PowerBroker2/UniversalTransmitter/extras/docs/4.jpg

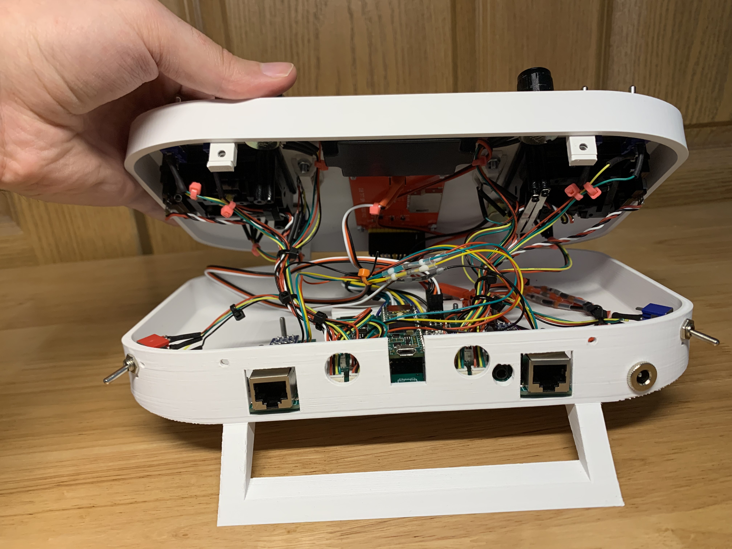
extras/docs/4.jpg
