PowerBroker2/UniversalTransmitter/examples/complex_example/SaveButton.h

#pragma once




const int SAVE_BUTTON_W = 40;
const int SAVE_BUTTON_H = 40;




const uint16_t saveButtonPixMap [SAVE_BUTTON_H * SAVE_BUTTON_W] PROGMEM = {
0x8410, 0x8410, 0x8410, 0x8410, 0x8410, 0x8410, 0x8410, 0x8410, 0x8410, 0x8410, 0x8410, 0x8410, 0x8410, 0x8410, 0x8410, 0x8410, 0x8410, 0x8410, 0x8410, 0x8410, 0x8410, 0x8410, 0x8410, 0x8410, 0x8410, 0x8410, 0x8410, 0x8410, 0x8410, 0x8410, 0x8410, 0x8410, 0x8410, 0x8410, 0x8410, 0x8410, 0x8410, 0x8410, 0x8410, 0x8410, 
0x8410, 0x8410, 0x8410, 0x8410, 0x8410, 0x8410, 0x8410, 0x8410, 0x8410, 0x8410, 0x8410, 0x8410, 0x8410, 0x8410, 0x8410, 0x8410, 0x8410, 0x8410, 0x8410, 0x8410, 0x8410, 0x8410, 0x8410, 0x8410, 0x8410, 0x8410, 0x8410, 0x8410, 0x8410, 0x8410, 0x8410, 0x8410, 0x8410, 0x8410, 0x8410, 0x8410, 0x8410, 0x8410, 0x8410, 0x8410, 
0x8410, 0x8410, 0x8410, 0x8410, 0x8410, 0x7bf0, 0x7bf0, 0x840f, 0x840f, 0x840f, 0x840f, 0x840f, 0x840f, 0x840f, 0x840f, 0x840f, 0x840f, 0x840f, 0x840f, 0x840f, 0x840f, 0x840f, 0x840f, 0x840f, 0x840f, 0x840f, 0x840f, 0x840f, 0x840f, 0x840f, 0x840f, 0x840f, 0x840f, 0x7bf0, 0x8410, 0x8410, 0x8410, 0x8410, 0x8410, 0x8410, 
0x8410, 0x8410, 0x8410, 0x8410, 0x7bf0, 0x840f, 0x8c4f, 0x842f, 0x842f, 0x842f, 0x842f, 0x842f, 0x842f, 0x842f, 0x842f, 0x842f, 0x842f, 0x842f, 0x842f, 0x842f, 0x842f, 0x842f, 0x842f, 0x842f, 0x842f, 0x842f, 0x842f, 0x842f, 0x842f, 0x842f, 0x842f, 0x842f, 0x8c4f, 0x842f, 0x7bf0, 0x7bf0, 0x8410, 0x8410, 0x8410, 0x8410, 
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
0,0,0,0,0,0,0,0,0,0,0,0,0,0,0,0,0,0,0,0,0,0,0,0,0,0,0,0,0,0,0,0,0,0,0,0,0,0,0,0,
0,0,0,0,0,0,0,0,0,0,0,0,0,0,0,0,0,0,0,0,0,0,0,0,0,0,0,0,0,0,0,0,0,0,0,0,0,0,0,0,
0,0,0,0,0,0,0,0,0,0,0,0,0,0,0,0,0,0,0,0,0,0,0,0,0,0,0,0,0,0,0,0,0,0,0,0,0,0,0,0
};
