PowerBroker2/UniversalTransmitter/examples/complex_example/button.h

#pragma once




const int BUTTON_W = 89;
const int BUTTON_H = 40;




const uint16_t buttonPixMap [BUTTON_H * BUTTON_W] PROGMEM = {
0x8410, 0x8410, 0x8410, 0x8410, 0x8410, 0x8410, 0x7bef, 0x8410, 0x7bef, 0x7bef, 0x8c51, 0x9492, 0x7bef, 0x4a69, 0x2104, 0x0020, 0x0000, 0x0000, 0x0000, 0x0000, 0x0000, 0x0000, 0x0000, 0x0000, 0x0000, 0x0000, 0x0000, 0x0000, 0x0000, 0x0000, 0x0000, 0x0000, 0x0000, 0x0000, 0x0000, 0x0000, 0x0000, 0x0000, 0x0000, 0x0000, 0x0000, 0x0000, 0x0000, 0x0000, 0x0000, 0x0000, 0x0000, 0x0000, 0x0000, 0x0000, 0x0000, 0x0000, 0x0000, 0x0000, 0x0000, 0x0000, 0x0000, 0x0000, 0x0000, 0x0000, 0x0000, 0x0000, 0x0000, 0x0000, 0x0000, 0x0000, 0x0000, 0x0000, 0x0000, 0x0000, 0x0000, 0x0000, 0x0000, 0x0020, 0x2104, 0x4a69, 0x7bef, 0x9492, 0x8c51, 0x7bef, 0x7bef, 0x8410, 0x7bef, 0x8410, 0x8410, 0x8410, 0x8410, 0x8410, 0x8410, 
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
0,0,0,0,0,0,0,0,0,0,0,0,0,0,0,0,0,0,1,1,1,1,1,1,1,1,1,1,1,1,1,1,1,1,1,1,1,1,1,1,1,1,1,1,1,1,1,1,1,1,1,1,1,1,1,1,1,1,1,1,1,1,1,1,1,1,1,1,1,1,1,0,0,0,0,0,0,0,0,0,0,0,0,0,0,0,0,0,0
};
