PowerBroker2/UniversalTransmitter/examples/complex_example/wide_button.h

#pragma once




const int WIDE_BUTTON_W = 180;
const int WIDE_BUTTON_H = 40;




const uint16_t wideButtonPixMap [WIDE_BUTTON_H * WIDE_BUTTON_W] PROGMEM = {
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
};
