PowerBroker2/UniversalTransmitter/examples/complex_example/CheckButton.h

#pragma once




const int CHECK_BUTTON_W = 20;
const int CHECK_BUTTON_H = 20;




const uint16_t checkButtonPixMap [CHECK_BUTTON_H * CHECK_BUTTON_W] PROGMEM = {
0x8410, 0x8410, 0x8410, 0x8410, 0x8410, 0x8410, 0x8410, 0x8410, 0x8410, 0x8410, 0x8410, 0x8410, 0x8410, 0x8410, 0x8410, 0x7bef, 0x8410, 0x9cf3, 0x5acb, 0x18c3, 
0x8410, 0x8410, 0x8410, 0x8410, 0x8410, 0x8410, 0x8410, 0x8410, 0x8410, 0x8410, 0x8410, 0x8410, 0x8410, 0x8410, 0x7bef, 0x8410, 0x8c71, 0x4228, 0x18e3, 0x73ae, 
0x8410, 0x8410, 0x8410, 0x8410, 0x8410, 0x8410, 0x8410, 0x8410, 0x8410, 0x8410, 0x8410, 0x8410, 0x8410, 0x7bef, 0x8430, 0x8bf1, 0x29c5, 0x0080, 0x7bcf, 0x9492, 
0x8410, 0x8410, 0x8410, 0x8410, 0x8410, 0x8410, 0x8410, 0x8410, 0x8410, 0x8410, 0x8410, 0x8410, 0x7bef, 0x8c51, 0x8390, 0x1a03, 0x0160, 0x7bcf, 0x8c51, 0x7bef, 
0x8410, 0x8410, 0x8410, 0x8410, 0x8410, 0x8410, 0x8410, 0x8410, 0x8410, 0x8410, 0x8410, 0x7bef, 0x8c51, 0x7b4f, 0x1242, 0x0240, 0x734e, 0x8c51, 0x7bef, 0x8410, 
0x8410, 0x8410, 0x8410, 0x8410, 0x8410, 0x8410, 0x8410, 0x8410, 0x8410, 0x8410, 0x7bef, 0x8c51, 0x7b2f, 0x1262, 0x0300, 0x62ac, 0x8c51, 0x7bef, 0x8410, 0x8410, 
0x8410, 0x8410, 0x8410, 0x8410, 0x8410, 0x8410, 0x8410, 0x8410, 0x8410, 0x7bef, 0x8450, 0x7b4f, 0x1242, 0x03e0, 0x4a29, 0x9451, 0x7bef, 0x8410, 0x8410, 0x8410, 
0x8410, 0x8410, 0x8410, 0x8410, 0x8410, 0x8410, 0x8410, 0x8410, 0x7bef, 0x8430, 0x83b0, 0x1a03, 0x04c0, 0x2a05, 0x8c11, 0x8410, 0x7bef, 0x8410, 0x8410, 0x8410, 
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
0,0,118,255,247,146,255,255,255,50,0,0,0,0,0,0,0,0,0,0,
0,0,0,168,255,255,255,255,186,0,0,0,0,0,0,0,0,0,0,0,
0,0,0,0,216,255,255,255,43,0,0,0,0,0,0,0,0,0,0,0,
0,0,0,0,27,247,255,184,0,0,0,0,0,0,0,0,0,0,0,0,
0,0,0,0,0,67,245,51,0,0,0,0,0,0,0,0,0,0,0,0,
0,0,0,0,0,0,133,2,0,0,0,0,0,0,0,0,0,0,0,0
};
