PowerBroker2/UniversalTransmitter/examples/complex_example/DownButton.h

#pragma once




const int DOWN_BUTTON_W = 20;
const int DOWN_BUTTON_H = 20;




const uint16_t downButtonPixMap [DOWN_BUTTON_H * DOWN_BUTTON_W] PROGMEM = {
0x8410, 0x8410, 0x8410, 0x8410, 0x8410, 0x7bf0, 0x840f, 0x942f, 0x8bee, 0x738e, 0x738d, 0x83ce, 0x942f, 0x8c0f, 0x7bf0, 0x8410, 0x8410, 0x8410, 0x8410, 0x8410, 
0x8410, 0x8410, 0x8410, 0x7bf0, 0x8410, 0x8c0f, 0x6b8e, 0x536f, 0x53d2, 0x5c34, 0x5c54, 0x53f3, 0x5390, 0x636e, 0x83ef, 0x840f, 0x7bf0, 0x8410, 0x8410, 0x8410, 
0x8410, 0x8410, 0x7bf0, 0x840f, 0x7bcf, 0x4350, 0x6cd6, 0xae7c, 0xbefe, 0xbf1f, 0xaede, 0xa69d, 0x9e3c, 0x7538, 0x4bb1, 0x73ae, 0x8c0f, 0x7bf0, 0x8410, 0x8410, 
0x8410, 0x7bf0, 0x840f, 0x73ae, 0x4392, 0xae7c, 0xdf9f, 0xbf1f, 0x9e9d, 0x8e3d, 0x7dfc, 0x6dbc, 0x6dbc, 0x7dfc, 0x963c, 0x5c54, 0x638e, 0x8c0f, 0x7bf0, 0x8410, 
0x8410, 0x840f, 0x7bce, 0x4392, 0xc71e, 0xc75f, 0x9e9d, 0x967d, 0x863d, 0x7dfc, 0x6dbb, 0x5d7b, 0x553a, 0x3cd9, 0x2c99, 0x861c, 0x5c75, 0x6b8e, 0x840f, 0x7bf0, 
0x7bf0, 0x8c0f, 0x4350, 0xa67c, 0xbf3f, 0x967d, 0x8e5d, 0x861c, 0x75dc, 0x659b, 0x5d5b, 0x4d1a, 0x3499, 0x1c38, 0x0bf7, 0x03b6, 0x7ddb, 0x53d2, 0x83ef, 0x7bf0, 
0x840f, 0x6b8e, 0x6cb6, 0xc75f, 0x8e5d, 0x861d, 0x75dc, 0x6dbc, 0x657b, 0x553a, 0x2c99, 0x1418, 0x0bf7, 0x03b6, 0x0396, 0x0395, 0x2437, 0x7d59, 0x5b6f, 0x8c2f, 
0x942f, 0x536f, 0x9e5c, 0x9e9e, 0x7dfc, 0x75fc, 0x7dfc, 0x4d3a, 0x44fa, 0x1438, 0x03f7, 0x0bf7, 0x0396, 0x2457, 0x1c17, 0x0375, 0x0354, 0x6559, 0x63f2, 0x940e, 
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
0,0,0,38,237,255,255,255,255,255,255,255,255,255,255,255,78,0,0,0,
0,0,0,0,27,190,255,255,255,255,255,255,255,255,216,57,0,0,0,0,
0,0,0,0,0,0,71,170,224,241,242,230,185,93,0,0,0,0,0,0,
0,0,0,0,0,0,0,0,0,33,37,3,0,0,0,0,0,0,0,0
};
