PowerBroker2/UniversalTransmitter/examples/complex_example/LeftButton.h

#pragma once




const int LEFT_BUTTON_W = 20;
const int LEFT_BUTTON_H = 20;




const uint16_t leftButtonPixMap [LEFT_BUTTON_H * LEFT_BUTTON_W] PROGMEM = {
0x8410, 0x8410, 0x8410, 0x8410, 0x8410, 0x7bf0, 0x840f, 0x942f, 0x8bee, 0x7bae, 0x7bae, 0x8bee, 0x942f, 0x840f, 0x7bf0, 0x8410, 0x8410, 0x8410, 0x8410, 0x8410, 
0x8410, 0x8410, 0x8410, 0x7bf0, 0x8410, 0x8c0f, 0x6b8e, 0x536f, 0x53b2, 0x5c13, 0x5c13, 0x53d2, 0x5390, 0x6b8e, 0x8c0f, 0x8410, 0x7bf0, 0x8410, 0x8410, 0x8410, 
0x8410, 0x8410, 0x7bf0, 0x840f, 0x7bcf, 0x4350, 0x64b6, 0xa65c, 0xbefe, 0xb6fe, 0xaede, 0xa69d, 0x961b, 0x6cf7, 0x4b90, 0x73ae, 0x840f, 0x7bf0, 0x8410, 0x8410, 
0x8410, 0x7bf0, 0x840f, 0x73ae, 0x4392, 0xae7c, 0xdf9f, 0xbf3f, 0x9e9e, 0x8e3d, 0x7dfc, 0x6ddc, 0x6ddc, 0x861c, 0x961c, 0x5413, 0x6b8e, 0x840f, 0x7bf0, 0x8410, 
0x8410, 0x840f, 0x7bce, 0x4392, 0xc71e, 0xc75f, 0x9e9d, 0x967d, 0x8e3d, 0x75dc, 0x659b, 0x555a, 0x553a, 0x3cb9, 0x34b9, 0x8e1c, 0x5414, 0x73ae, 0x840f, 0x7c10, 
0x7bf0, 0x8c0f, 0x4350, 0xae9d, 0xbf3f, 0x967d, 0x8e5d, 0x861c, 0x6dbc, 0x555b, 0xbedd, 0xae9d, 0x2c99, 0x1c38, 0x0bf7, 0x0bd6, 0x7ddb, 0x53b1, 0x83ef, 0x7bf0, 
0x840f, 0x636e, 0x6cd7, 0xc75f, 0x8e5d, 0x863d, 0x7dfc, 0x659b, 0x4d3a, 0xaebd, 0xffff, 0xe79e, 0x1c38, 0x03b6, 0x0bd6, 0x0375, 0x2c78, 0x7538, 0x638f, 0x8c0f, 
0x942f, 0x5370, 0xa67c, 0x9e9e, 0x861d, 0x75dc, 0x659b, 0x451a, 0xa69d, 0xffdf, 0xdf7e, 0x2c78, 0x03b6, 0x0bd6, 0x0bd6, 0x0bb5, 0x0374, 0x6d79, 0x63d1, 0x942f, 
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
0,0,0,57,250,255,255,255,255,255,255,255,255,255,255,255,76,0,0,0,
0,0,0,0,44,209,255,255,255,255,255,255,255,255,219,58,0,0,0,0,
0,0,0,0,0,0,90,187,233,245,246,235,193,100,1,0,0,0,0,0,
0,0,0,0,0,0,0,0,11,51,53,15,0,0,0,0,0,0,0,0
};
