PowerBroker2/UniversalTransmitter/examples/complex_example/RightButton.h

#pragma once




const int RIGHT_BUTTON_W = 20;
const int RIGHT_BUTTON_H = 20;




const uint16_t rightButtonPixMap [RIGHT_BUTTON_H * RIGHT_BUTTON_W] PROGMEM = {
0x8410, 0x8410, 0x8410, 0x8410, 0x7c10, 0x7bf0, 0x8c0f, 0x940f, 0x738e, 0x5b2d, 0x530d, 0x634d, 0x8bee, 0x942f, 0x8410, 0x7bf0, 0x8410, 0x8410, 0x8410, 0x8410, 
0x8410, 0x8410, 0x8410, 0x7bf0, 0x8410, 0x83ef, 0x5b6e, 0x4b91, 0x5c34, 0x6cb6, 0x6cd6, 0x6475, 0x53f2, 0x536f, 0x7bce, 0x8c0f, 0x7bf0, 0x8410, 0x8410, 0x8410, 
0x8410, 0x8410, 0x7bf0, 0x840f, 0x73ae, 0x4371, 0x7d58, 0xbefe, 0xc73f, 0xbf1f, 0xaefe, 0xa6be, 0x9e7d, 0x8dda, 0x5434, 0x5b6f, 0x8c0f, 0x7bf0, 0x8410, 0x8410, 
0x8410, 0x7bf0, 0x840f, 0x6b8e, 0x43d3, 0xbefe, 0xd79f, 0xaefe, 0x965d, 0x861c, 0x7dfc, 0x6d9b, 0x5d7b, 0x65bb, 0x8e3d, 0x6cf7, 0x536f, 0x8c0f, 0x7bf0, 0x8410, 
0x8410, 0x840f, 0x7bce, 0x43b2, 0xcf5f, 0xbf3f, 0x9e7d, 0x965d, 0x861c, 0x7dfc, 0x659b, 0x5d7b, 0x553a, 0x3cd9, 0x1c58, 0x659b, 0x6d18, 0x5b6f, 0x8c0f, 0x7bf0, 
0x7bf0, 0x8c0f, 0x4350, 0xae9d, 0xbf3f, 0x967d, 0x8e3d, 0x7dfc, 0xc71e, 0xcf3e, 0x555a, 0x3cd9, 0x2c98, 0x1437, 0x0bf7, 0x0375, 0x657a, 0x6454, 0x73ae, 0x840f, 
0x840f, 0x6b8e, 0x64b6, 0xc75f, 0x8e3d, 0x863d, 0x75dc, 0x6dbb, 0xcf1e, 0xf7df, 0xbedd, 0x1418, 0x03b6, 0x0bd7, 0x0bd6, 0x03b6, 0x0bd6, 0x7d9a, 0x5b90, 0x942f, 
0x942f, 0x536f, 0x9e3b, 0x9e9e, 0x7e1d, 0x6ddc, 0x659b, 0x553b, 0x34da, 0xae9d, 0xf7df, 0xbedd, 0x0bd7, 0x0396, 0x0bd6, 0x0bb5, 0x0334, 0x5519, 0x6454, 0x83ae, 
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
0,0,0,187,255,255,255,255,255,255,255,255,255,255,255,255,253,36,0,0,
0,0,0,4,193,255,255,255,255,255,255,255,255,255,255,247,62,0,0,0,
0,0,0,0,0,136,252,255,255,255,255,255,255,255,192,37,0,0,0,0,
0,0,0,0,0,0,27,118,187,218,222,202,149,61,0,0,0,0,0,0,
0,0,0,0,0,0,0,0,0,0,0,0,0,0,0,0,0,0,0,0
};
