PowerBroker2/UniversalTransmitter/examples/complex_example/UpButton.h

#pragma once




const int UP_BUTTON_W = 20;
const int UP_BUTTON_H = 20;




const uint16_t upButtonPixMap [UP_BUTTON_H * UP_BUTTON_W] PROGMEM = {
0x8410, 0x8410, 0x8410, 0x8410, 0x8410, 0x7bf0, 0x840f, 0x942f, 0x83ce, 0x6b6d, 0x6b6d, 0x7bae, 0x942f, 0x8c0f, 0x7bf0, 0x7c10, 0x8410, 0x8410, 0x8410, 0x8410, 
0x8410, 0x8410, 0x8410, 0x7bf0, 0x8410, 0x8c0f, 0x636e, 0x4b70, 0x53f2, 0x5c54, 0x6454, 0x5c13, 0x5390, 0x636e, 0x83ef, 0x840f, 0x7bf0, 0x8410, 0x8410, 0x8410, 
0x8410, 0x8410, 0x7bf0, 0x840f, 0x73ae, 0x4350, 0x7517, 0xb69d, 0xbf1e, 0xbf1f, 0xaede, 0xa69e, 0x9e5c, 0x7d38, 0x4bb1, 0x73ae, 0x8c0f, 0x7bf0, 0x8410, 0x8410, 
0x8410, 0x7bf0, 0x840f, 0x6b8e, 0x43b3, 0xb6bd, 0xdf9f, 0xb71f, 0x9e7d, 0x863d, 0x7dfc, 0x6dbb, 0x659b, 0x7dfc, 0x963c, 0x5c55, 0x638e, 0x8c0f, 0x7bf0, 0x8410, 
0x8410, 0x840f, 0x7bae, 0x43b3, 0xcf5f, 0xc73f, 0x9e7d, 0x965d, 0x863c, 0x7dfc, 0x6dbb, 0x5d7b, 0x553a, 0x3cb9, 0x2c98, 0x861c, 0x5c55, 0x6b8e, 0x840f, 0x7bf0, 
0x7bf0, 0x8c0f, 0x4350, 0xb6bd, 0xbf1f, 0x967d, 0x8e5d, 0x7e1c, 0x75dc, 0x5d5b, 0x4d1a, 0x44fa, 0x2c99, 0x1c38, 0x0bf7, 0x03b6, 0x7ddb, 0x53d2, 0x83ef, 0x7bf0, 
0x840f, 0x636e, 0x6cf7, 0xc75f, 0x8e5d, 0x863d, 0x75fc, 0x6dbc, 0x4d1a, 0x7dfc, 0x7ddb, 0x03b7, 0x0bf7, 0x0bd7, 0x0bd6, 0x0395, 0x2457, 0x7d58, 0x636f, 0x8c0f, 
0x942f, 0x5370, 0xa67c, 0x969e, 0x7e1d, 0x75dc, 0x659b, 0x44fa, 0x659b, 0xdf7e, 0xefbf, 0x5d5a, 0x0376, 0x0bd6, 0x0bd6, 0x0bb5, 0x0354, 0x6d59, 0x63f2, 0x940f, 
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
0,0,0,38,236,255,255,255,255,255,255,255,255,255,255,251,63,0,0,0,
0,0,0,0,26,187,255,255,255,255,255,255,255,255,204,44,0,0,0,0,
0,0,0,0,0,0,66,164,220,237,238,223,174,80,0,0,0,0,0,0,
0,0,0,0,0,0,0,0,0,21,24,0,0,0,0,0,0,0,0,0
};
