PowerBroker2/UniversalTransmitter/examples/complex_example/XButton.h

#pragma once




const int X_BUTTON_W = 20;
const int X_BUTTON_H = 20;




const uint16_t xButtonPixMap [X_BUTTON_H * X_BUTTON_W] PROGMEM = {
0x8410, 0x7bef, 0x8410, 0x8492, 0x1186, 0x6c10, 0x8c30, 0x7bef, 0x8410, 0x8410, 0x8410, 0x8410, 0x7bef, 0x8c51, 0x63cf, 0x0945, 0x84b2, 0x8410, 0x7bef, 0x8410, 
0x7bef, 0x8410, 0x8492, 0x4a28, 0xa800, 0x5965, 0x7451, 0x8410, 0x7bef, 0x8410, 0x8410, 0x7bef, 0x8430, 0x6c51, 0x6124, 0xb000, 0x4a28, 0x8492, 0x8410, 0x7bef, 
0x8410, 0x8492, 0x4208, 0xb800, 0xf800, 0xe000, 0x4945, 0x7451, 0x8430, 0x7bef, 0x7bef, 0x8430, 0x6c51, 0x4904, 0xe800, 0xf800, 0xb800, 0x4208, 0x8492, 0x8410, 
0x84b2, 0x4228, 0xb800, 0xf800, 0xf000, 0xf800, 0xe000, 0x4945, 0x7471, 0x8410, 0x8410, 0x6c51, 0x4924, 0xe000, 0xf800, 0xf000, 0xf800, 0xb800, 0x4a28, 0x8492, 
0x0945, 0xb800, 0xf800, 0xf000, 0xf000, 0xf000, 0xf800, 0xe000, 0x4945, 0x7471, 0x7471, 0x4924, 0xe000, 0xf800, 0xf000, 0xf000, 0xf000, 0xf800, 0xb000, 0x0986, 
0x63cf, 0x6104, 0xe800, 0xf800, 0xf000, 0xf000, 0xf000, 0xf800, 0xe000, 0x4186, 0x4186, 0xe000, 0xf800, 0xf000, 0xf000, 0xf000, 0xf800, 0xe000, 0x5945, 0x6c10, 
0x8c51, 0x6c30, 0x50e3, 0xe800, 0xf800, 0xf000, 0xf000, 0xf000, 0xf800, 0xd800, 0xd800, 0xf800, 0xf000, 0xf000, 0xf000, 0xf800, 0xe000, 0x4924, 0x6c51, 0x8c51, 
0x7bef, 0x8430, 0x6c30, 0x5104, 0xe800, 0xf800, 0xf000, 0xf000, 0xf000, 0xf800, 0xf800, 0xf000, 0xf000, 0xf000, 0xf800, 0xe800, 0x4924, 0x6c51, 0x8430, 0x7bef, 
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
0,112,255,255,255,255,255,184,0,0,0,0,173,255,255,255,255,255,110,0,
0,0,114,255,255,255,185,0,0,0,0,0,0,170,255,255,255,116,0,0,
0,0,0,109,251,182,0,0,0,0,0,0,0,0,165,251,114,0,0,0,
0,0,0,0,154,10,0,0,0,0,0,0,0,0,0,144,0,0,0,0
};
